facebookarchive/opencompute/AMD_server_V2/images/amd_hardDrivePower.png

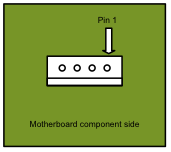
AMD_server_V2/images/amd_hardDrivePower.png
