facebookarchive/opencompute/Intel_server_V2/images/intel_en_placement.png

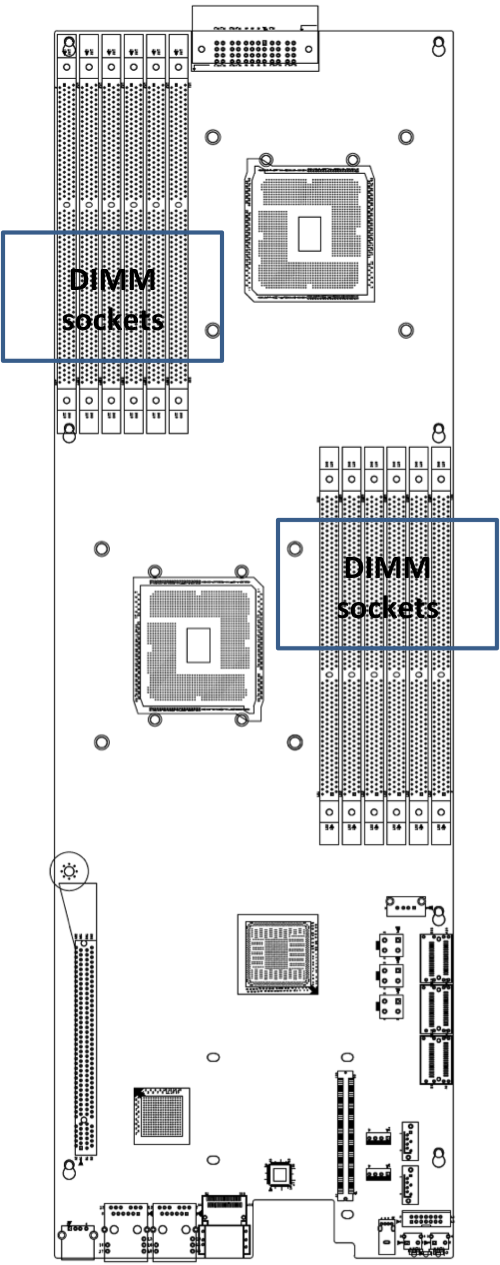
Intel_server_V2/images/intel_en_placement.png
