facebookarchive/opencompute/Intel_server_V2/images/intel_ep_block.png

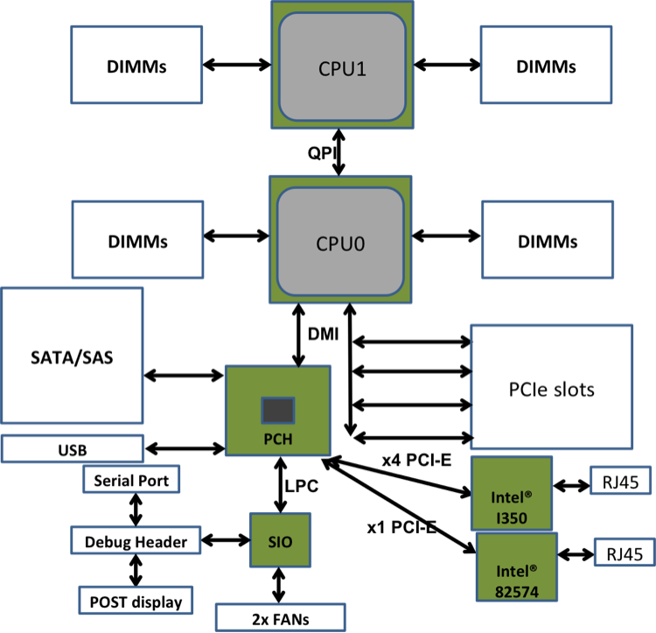
Intel_server_V2/images/intel_ep_block.png
