facebookarchive/opencompute/Intel_server_V2/images/intel_ep_placement.png

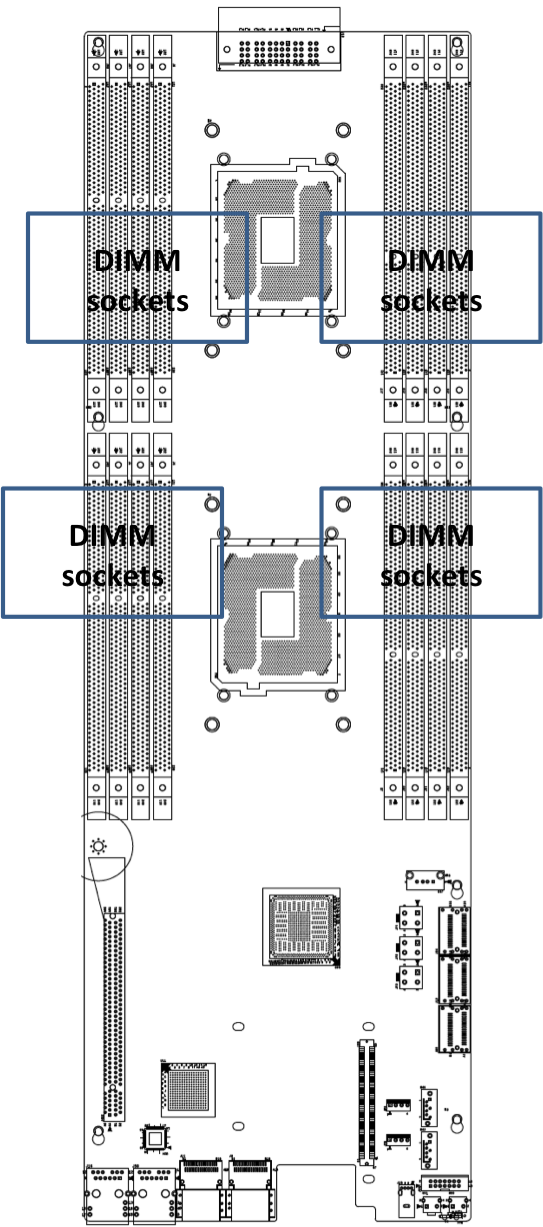
Intel_server_V2/images/intel_ep_placement.png
