facebookarchive/opencompute/Intel_server_V2/images/intel_pcieRiser.png

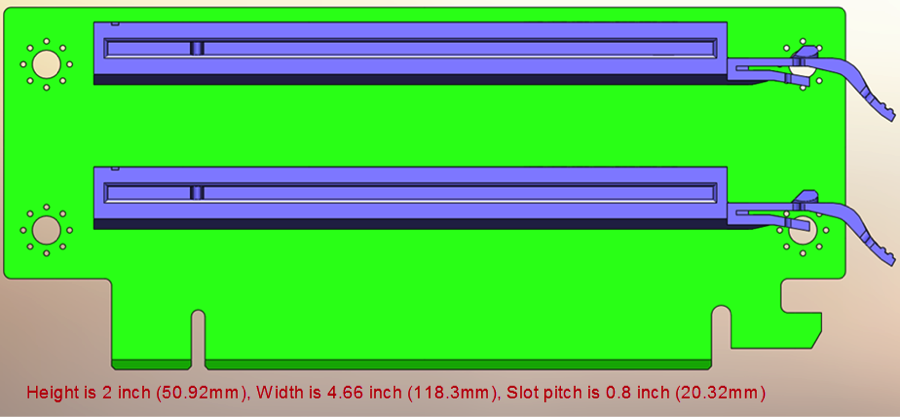
Intel_server_V2/images/intel_pcieRiser.png
