facebookarchive/opencompute/open_rack/images/single_col_front.png

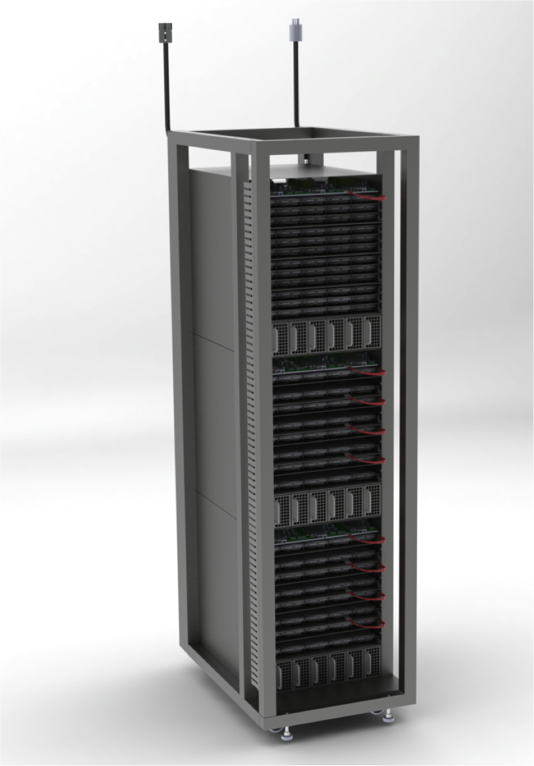
open_rack/images/single_col_front.png
