facebookarchive/opencompute/open_rack/images/single_col_rear_2bus.png

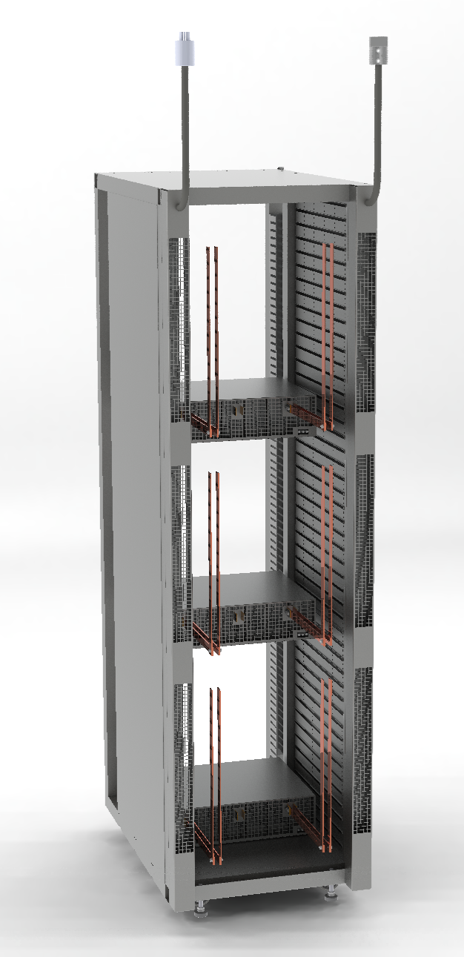
open_rack/images/single_col_rear_2bus.png
