facebookarchive/opencompute/open_rack/images/triplet_front.png

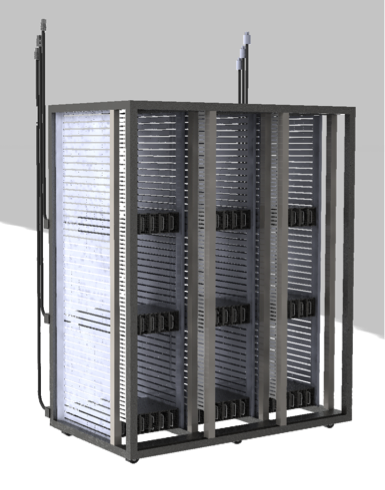
open_rack/images/triplet_front.png
