facebookarchive/opencompute/open_rack/images/triplet_front_control_drawing.png

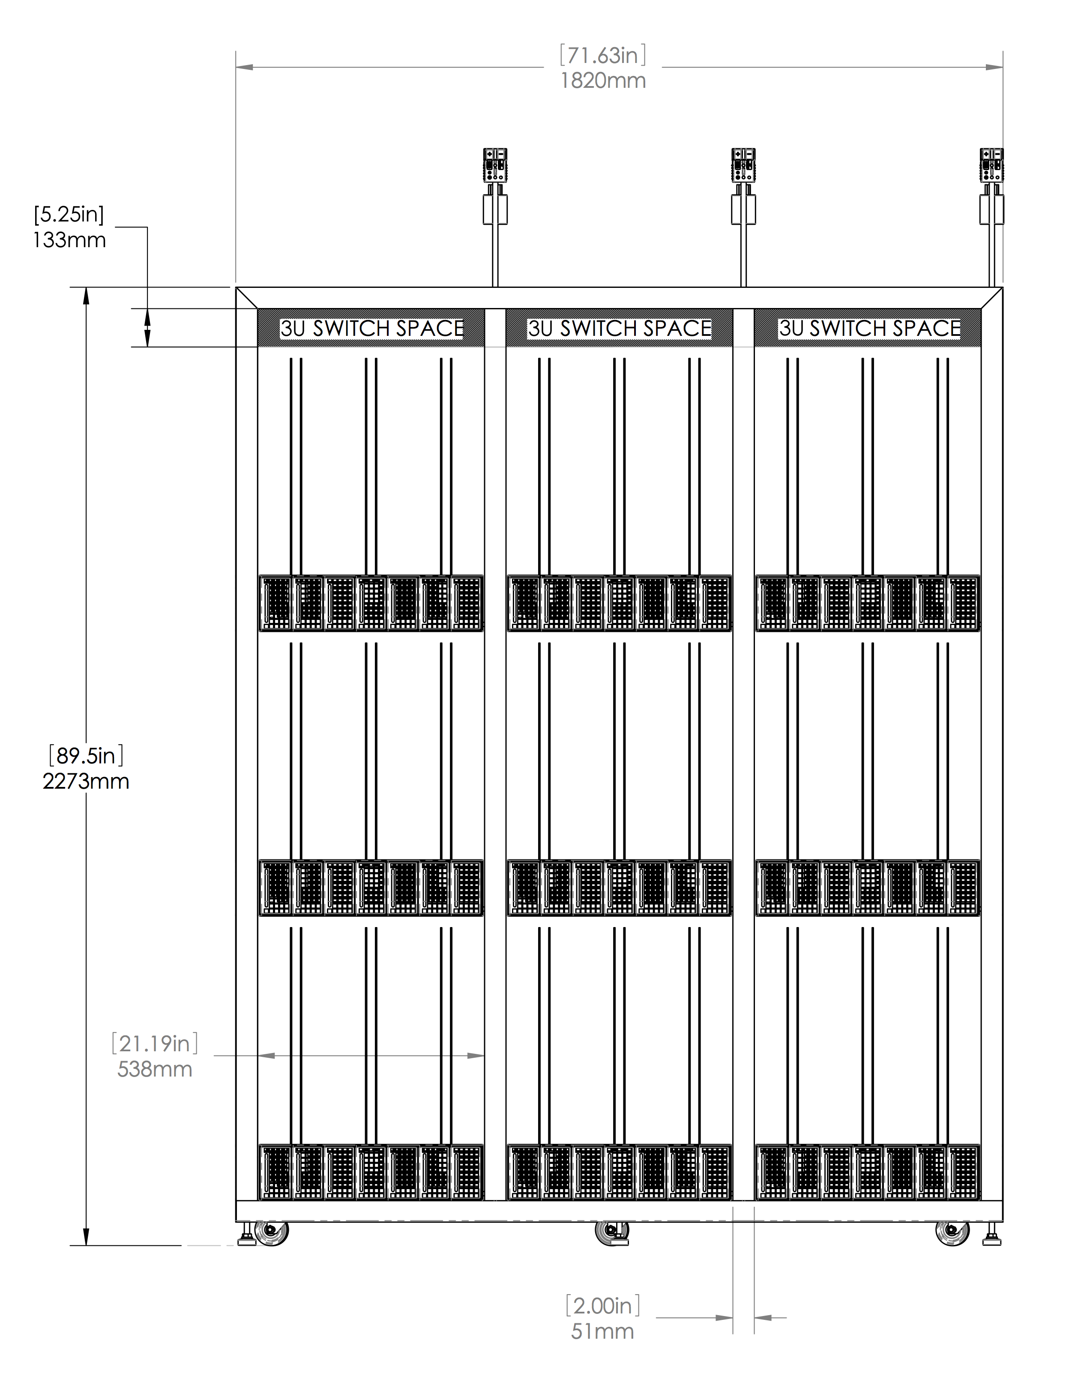
open_rack/images/triplet_front_control_drawing.png
