facebookarchive/opencompute/open_rack/images/triplet_front_section.png

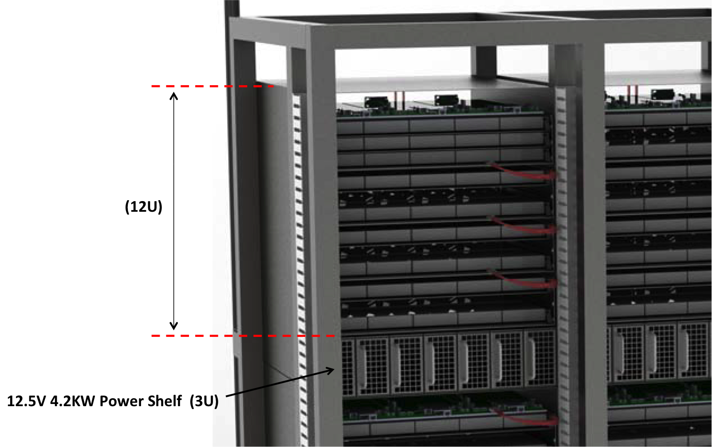
open_rack/images/triplet_front_section.png
