facebookarchive/opencompute/open_rack/images/triplet_rear.png

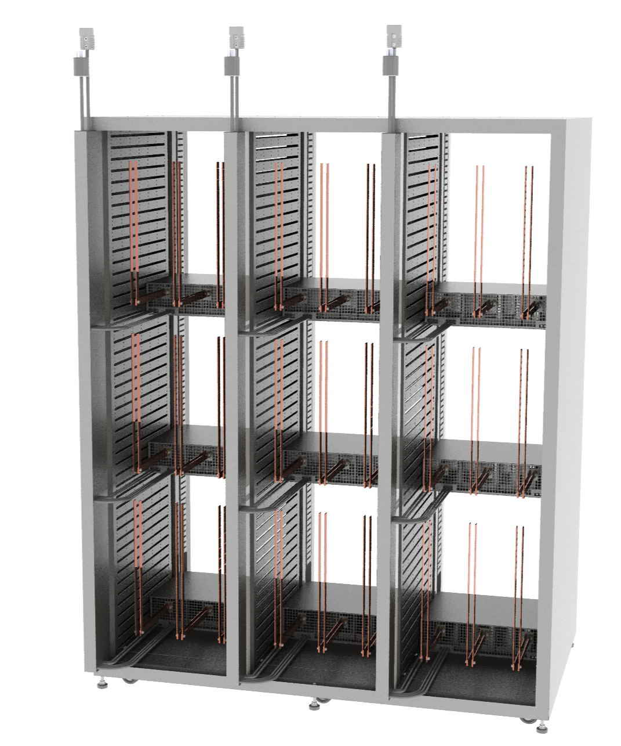
open_rack/images/triplet_rear.png
