facebookarchive/opencompute/open_rack/images/triplet_rear_control_drawing.png

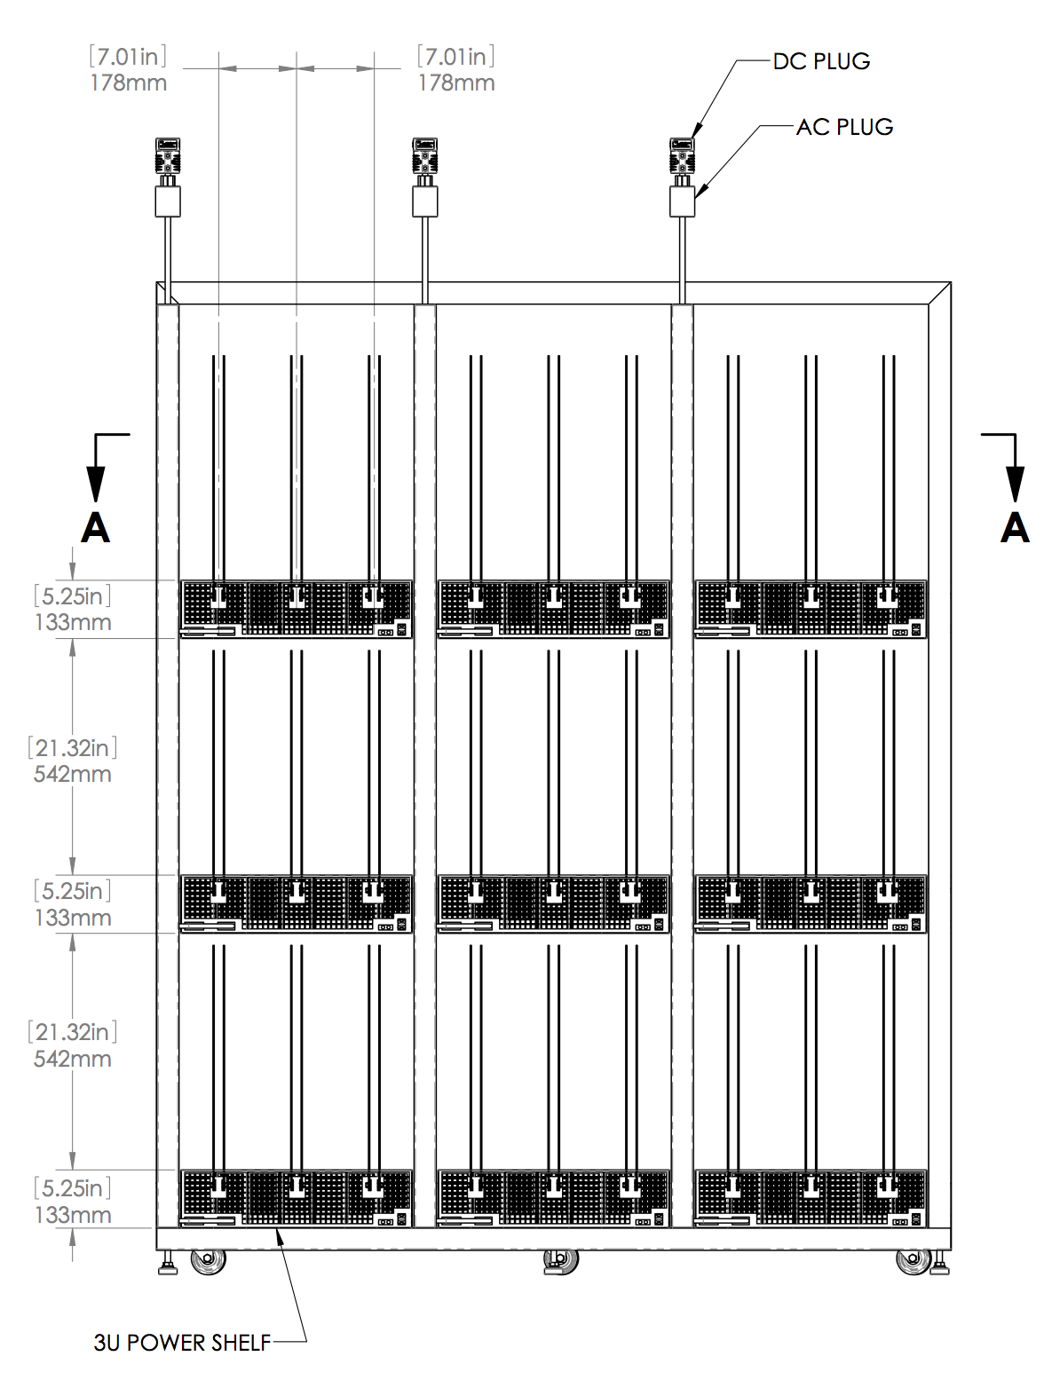
open_rack/images/triplet_rear_control_drawing.png
