facebookarchive/opencompute/open_rack/images/triplet_rear_hpdu.png

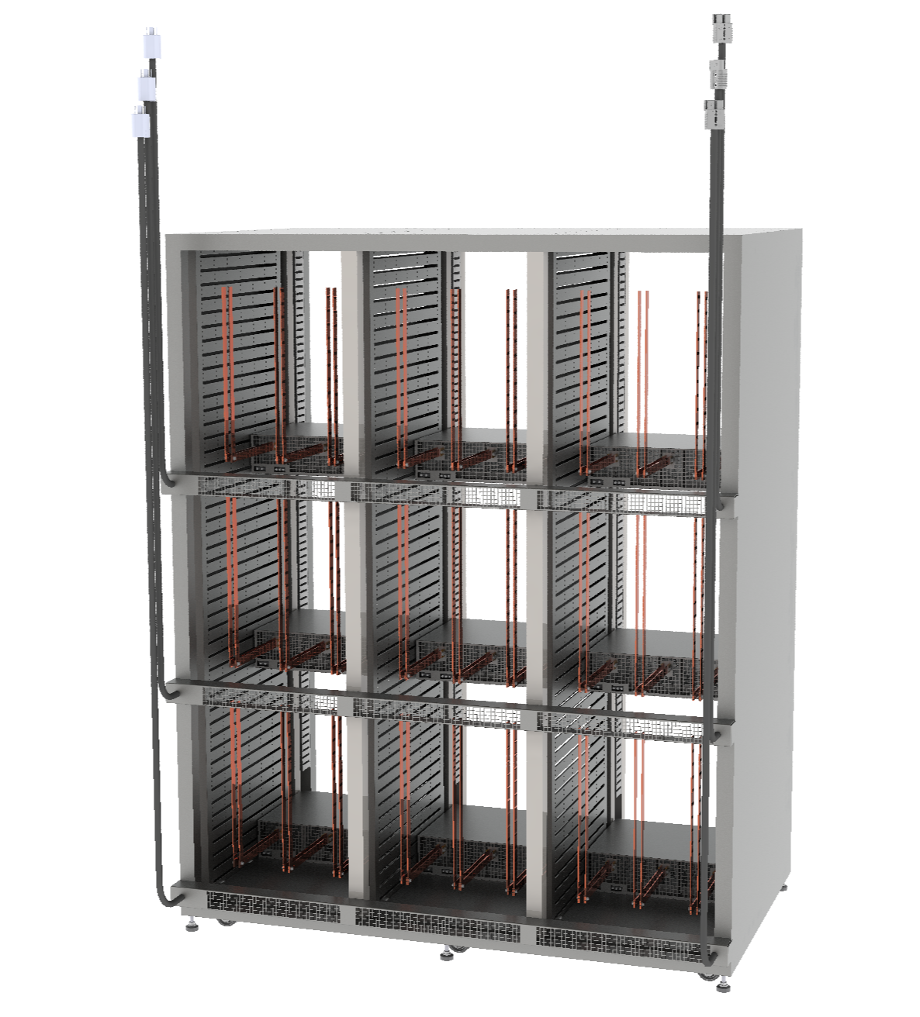
open_rack/images/triplet_rear_hpdu.png
