facebookarchive/opencompute/open_rack/images/triplet_rear_hpdu_annotated.png

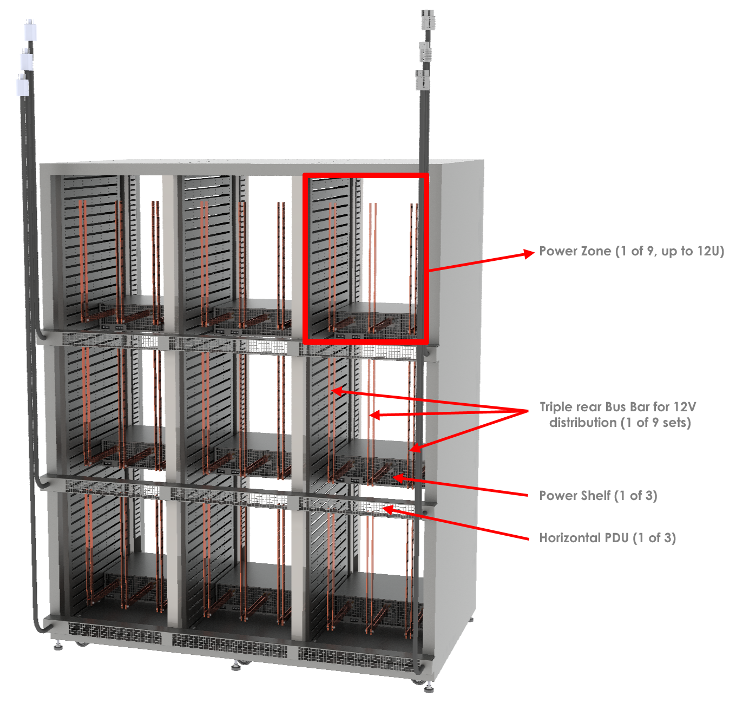
open_rack/images/triplet_rear_hpdu_annotated.png
