facebookarchive/opencompute/open_rack/images/v1_power_shelf.png

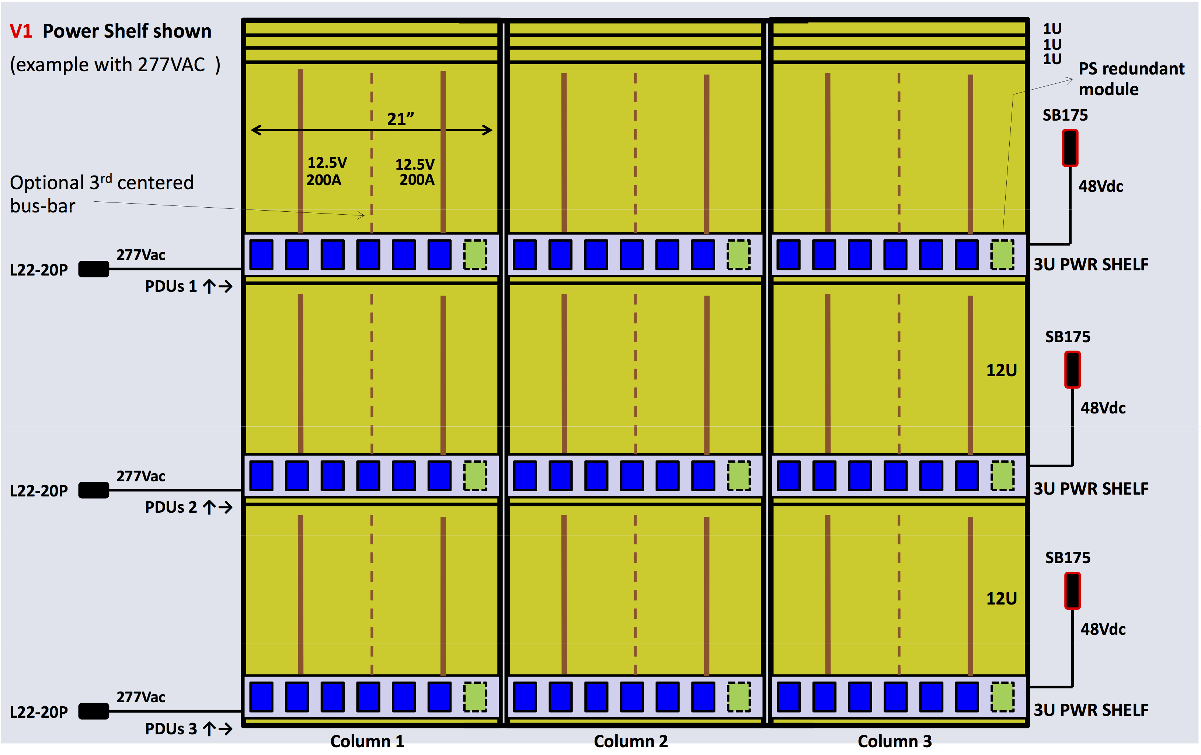
open_rack/images/v1_power_shelf.png
